sunriax/board/controller/ldr.asc

C1: cap; 470n
Q1: npn; 2N3904
R1: res; 80
R2: res; 3k3
R3: res; 10k
R4: res; 170
R5: res; 10k
V1: voltage; 5v
V2: signal; PULSE(0 5 0 1p 1p 0.5u 15u)
Named nets: 0, v+
.tran 0 80000u 70000u
